kitahei88/8-inch-FDD-interface/Doc/images/9.JPG

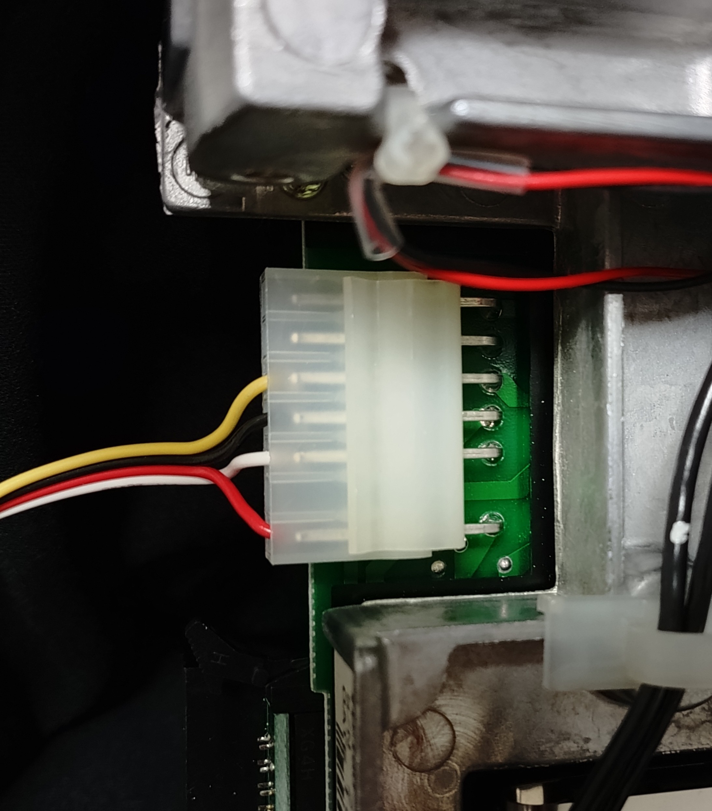
Doc/images/9.JPG
